tzurolo/Water-Tank-Monitor/firmware/InternalTemperatureMonitor.c

//
//  Internal Temperature Monitor
//
//  Reads the AtMega328P's internal temperature sensor through the ADC
//

#include "InternalTemperatureMonitor.h"

#include "ADCManager.h"
#include "SystemTime.h"
#include "DataHistory.h"
#include "EEPROMStorage.h"

#define SENSOR_ADC_CHANNEL ADC_SINGLE_ENDED_INPUT_TEMP

#define REFERENCE_VOLTAGE 1.1

#define RESOLUTION 1000
#define NUMERATOR ((int32_t)((1 / 0.94) * (1100 / 1024) * RESOLUTION))

#define SENSOR_SAMPLES 10
// sample 10 times per second (10 1/100ths)
#define SENSOR_SAMPLE_TIME 10

typedef enum {
    tms_idle,
    tms_waitingForADCStart,
    tms_waitingForADCCompletion
} TemperatureMonitor_state;

static TemperatureMonitor_state tmState = tms_idle;
static SystemTime_t sampleTimer;
DataHistory_define(SENSOR_SAMPLES, temperatureHistory);

void InternalTemperatureMonitor_Initialize (void)
{
    tmState = tms_idle;
    // start sampling in 1/50 second (20ms, to let power stabilize)
    SystemTime_futureTime(2, &sampleTimer);
    DataHistory_clear(&temperatureHistory);

    // set up the ADC channel for measuring battery voltage
    ADCManager_setupChannel(SENSOR_ADC_CHANNEL, ADC_VOLTAGE_REF_INTERNAL_1V1, false);
}

bool InternalTemperatureMonitor_haveValidSample (void)
{
    return DataHistory_length(&temperatureHistory) >= SENSOR_SAMPLES;
}

int16_t InternalTemperatureMonitor_currentTemperature (void)
{
    int16_t curTempC = 0;

    uint16_t avgTemperature = 0;
    if (InternalTemperatureMonitor_haveValidSample()) {
        uint16_t minTemmp;
        uint16_t maxTemp;
        DataHistory_getStatistics(
            &temperatureHistory, SENSOR_SAMPLES,
            &minTemmp, &maxTemp, &avgTemperature);

        int32_t temp = avgTemperature;
        // counts to degrees C
        const int16_t tempCalOffset = EEPROMStorage_tempCalOffset();
        curTempC = ((int16_t)(((temp - tempCalOffset) * NUMERATOR) / RESOLUTION));
    }

    return curTempC;
}

void InternalTemperatureMonitor_task (void)
{
    switch (tmState) {
        case tms_idle :
            if (SystemTime_timeHasArrived(&sampleTimer)) {
                SystemTime_futureTime(SENSOR_SAMPLE_TIME, &sampleTimer);
                tmState = tms_waitingForADCStart;
            }
            break;
        case tms_waitingForADCStart :
            if (ADCManager_StartConversion(SENSOR_ADC_CHANNEL)) {
                // successfully started conversion
                tmState = tms_waitingForADCCompletion;
            }
            break;    
        case tms_waitingForADCCompletion : {
            uint16_t batteryVoltage;
            if (ADCManager_ConversionIsComplete(&batteryVoltage)) {
                DataHistory_insertValue(batteryVoltage, &temperatureHistory);

                tmState = tms_idle;
            }
            }
            break;
    }
}
