tzurolo/Water-Tank-Monitor/firmware/CharStringSpan.c

//
//  Character String Range
//

#include "CharStringSpan.h"

void CharStringSpan_init (
    const CharString_t *str,
    CharStringSpan_t *span)
{
    span->m_begin = CharString_begin(str);
    span->m_end   = CharString_end(str);
}

void CharStringSpan_initRight (
    const CharString_t *str,
    const int offset,
    CharStringSpan_t *span)
{
    span->m_begin = CharString_begin(str) + offset;
    span->m_end   = CharString_end(str);
}

void CharStringSpan_extractLeft (
    const int numChars,
    CharStringSpan_t *span,
    CharStringSpan_t *left)
{
    const uint8_t spanLen = CharStringSpan_length(span);
    const int nChars = 
        (numChars < spanLen)
        ? numChars
        : spanLen;
    left->m_begin = span->m_begin;
    left->m_end = span->m_begin + nChars;
    span->m_begin += nChars;
}

char CharStringSpan_front(
    const CharStringSpan_t *span)
{
    return 
        (span->m_begin < span->m_end)
        ? *span->m_begin
        : 0;
}

void CharStringSpan_set (
    const CharString_Iter begin,
    const CharString_Iter end,
    CharStringSpan_t *span)
{
    span->m_begin = begin;
    span->m_end = end;
}

void CharStringSpan_incrBegin (
    CharStringSpan_t *span)
{
    if (span->m_begin < span->m_end) {
        ++span->m_begin;
    }
}

bool CharStringSpan_equalsP (
    const CharStringSpan_t* leftSpan,
    PGM_P rightStr)
{
    const int leftLen = CharStringSpan_length(leftSpan);
    return
        (leftLen == strlen_P(rightStr)) &&
        (strncmp_P(leftSpan->m_begin, rightStr, leftLen) == 0);
}

bool CharStringSpan_equalsNocaseP (
    const CharStringSpan_t* leftSpan,
    PGM_P rightStr)
{
    const int leftLen = CharStringSpan_length(leftSpan);
    return
        (leftLen == strlen_P(rightStr)) &&
        (strncasecmp_P(leftSpan->m_begin, rightStr, leftLen) == 0);
}

int CharStringSpan_compareP (
    const CharStringSpan_t* leftSpan,
    PGM_P rightStr)
{
    const int leftLen = CharStringSpan_length(leftSpan);
    const int rightLen = strlen_P(rightStr);
    if (leftLen == rightLen) {
        return strncmp_P(leftSpan->m_begin, rightStr, leftLen);
    } else {
        const int minLen =
            (leftLen < rightLen)
            ? leftLen
            : rightLen;
        int comp = strncmp_P(leftSpan->m_begin, rightStr, minLen);
        if (comp == 0) {
            return
                (leftLen < rightLen)
                ? -1
                : 1;
        } else {
            return comp;
        }
    }
}
