tzurolo/Water-Tank-Monitor/firmware/CommandProcessor.h

//
// Command processor
//
// Interprets and executes commands from SMS or the console
//

#ifndef COMMANDPROCESSOR_H
#define COMMANDPROCESSOR_H

#include <stdint.h>
#include <stdbool.h>
#include <string.h>
#include <stddef.h>
#include "CharStringSpan.h"

// buffer that clients can use to accumulate command characters
extern CharString_t CommandProcessor_incomingCommand;

// output from commands is put into this string
extern CharString_t CommandProcessor_commandReply;

// creates the status message in CommandProcessor_commandReply
extern void CommandProcessor_createStatusMessage (
    CharString_t *msg);

// writes response, if any, to CommandProcessor_commandReply
// returns true if given command is valid
extern bool CommandProcessor_executeCommand (
    const CharStringSpan_t* command,
    CharString_t *reply);

#endif  // COMMANDPROCESSOR_H
